sensestage/wearable_cape_v01/Documentation/Bela_Audio_Cape_Schematic.png

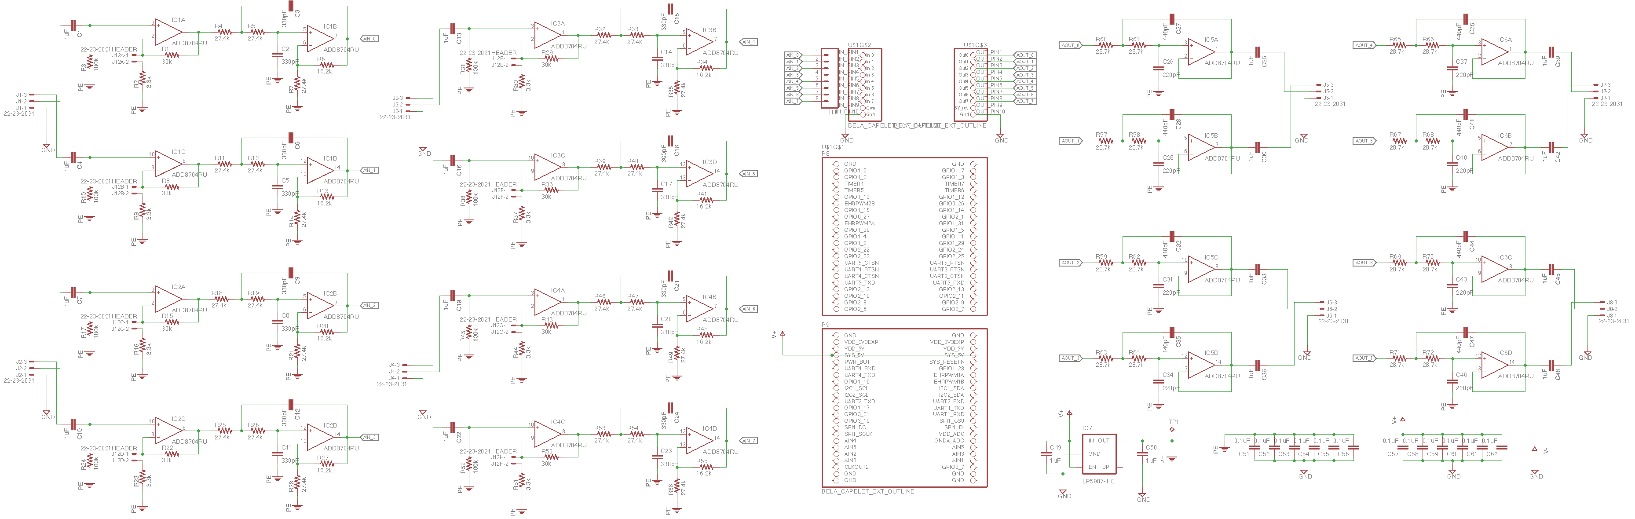
Documentation/Bela_Audio_Cape_Schematic.png
