sensestage/wearable_cape_v01/Documentation/Bela_Cape_Schematic01.png

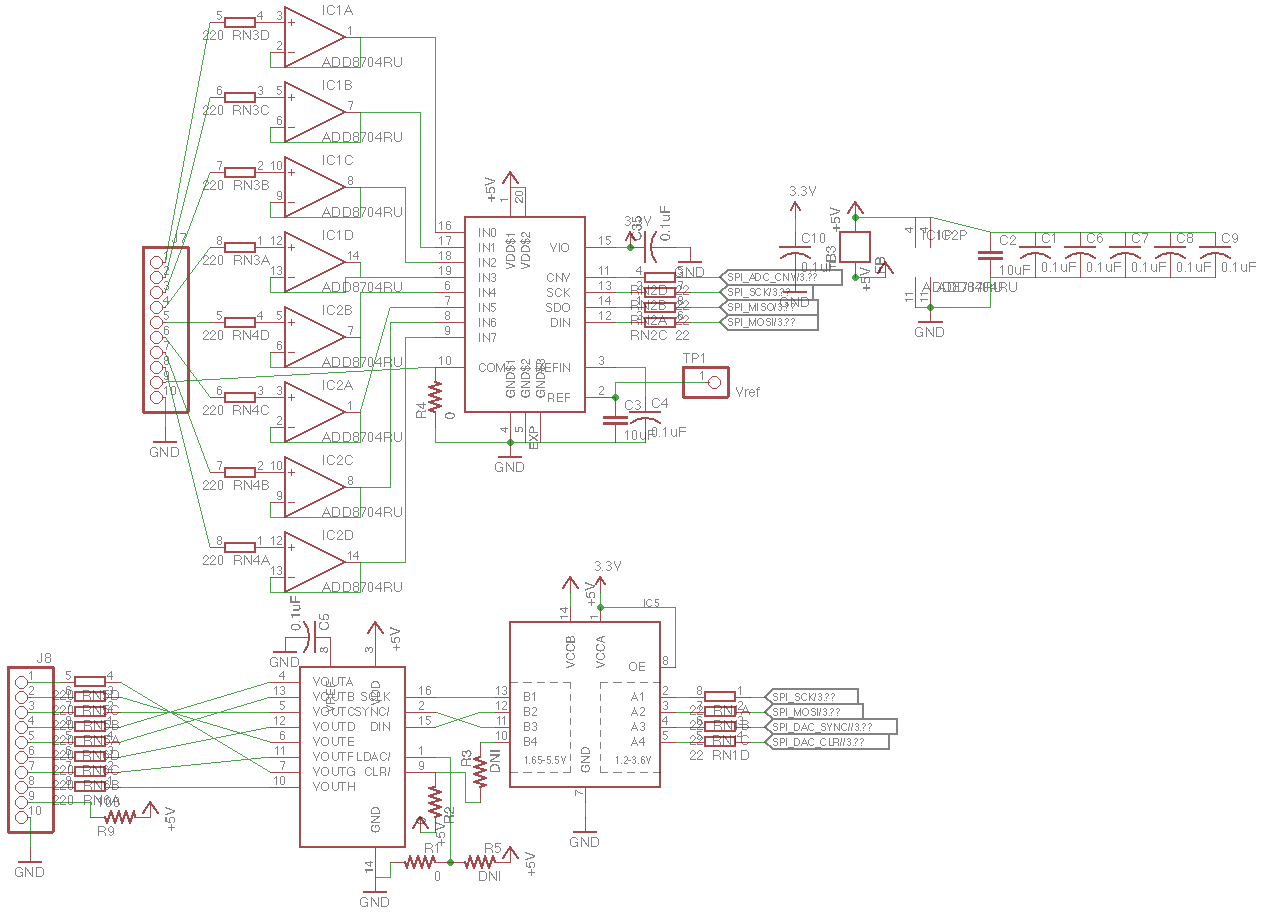
Documentation/Bela_Cape_Schematic01.png
