sensestage/wearable_cape_v01/Documentation/Datasheets/MAX9744_Adafruit_Inputs.png

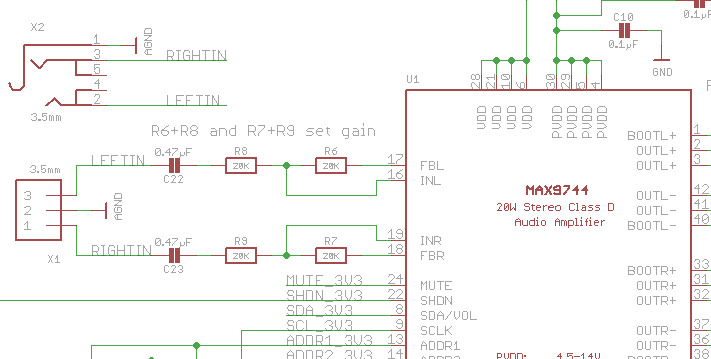
Documentation/Datasheets/MAX9744_Adafruit_Inputs.png
