sensestage/wearable_cape_v01/Documentation/Datasheets/MAX_9744_INPUTS.png

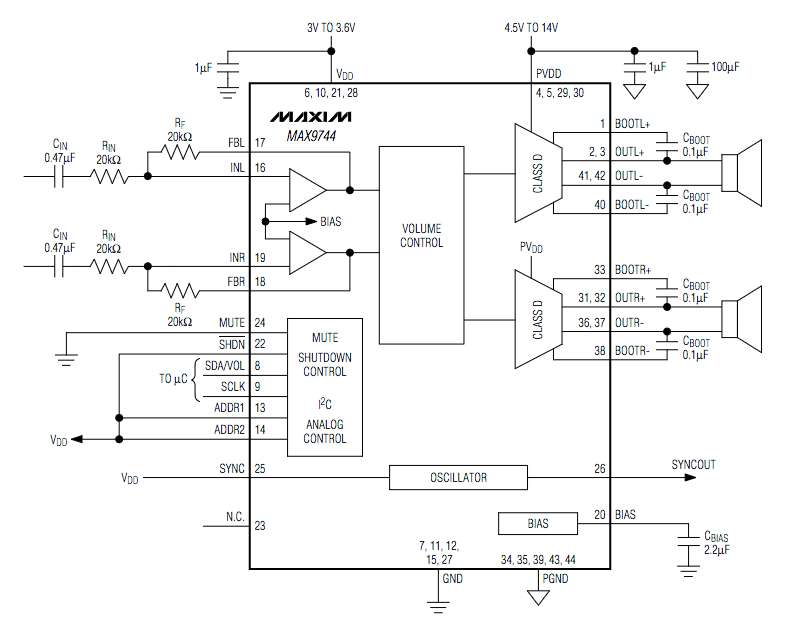
Documentation/Datasheets/MAX_9744_INPUTS.png
