sensestage/wearable_cape_v01/Documentation/earthquake_v01-PCB.png

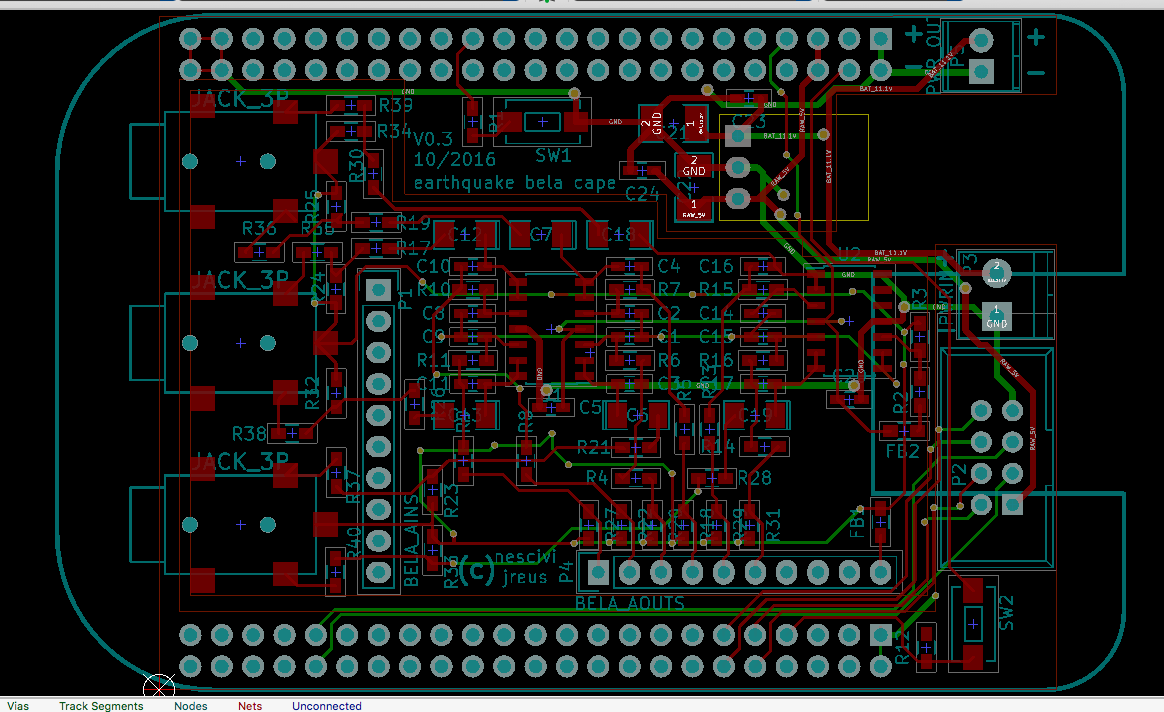
Documentation/earthquake_v01-PCB.png
