sensestage/wearable_cape_v01/Documentation/Simulations/Sallen-Key-Att-POST1.png

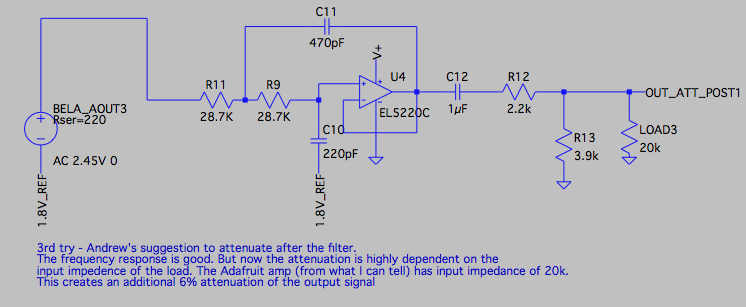
Documentation/Simulations/Sallen-Key-Att-POST1.png
