sensestage/wearable_cape_v01/Documentation/Simulations/Sallen-Key-Att-POST1_SER.png

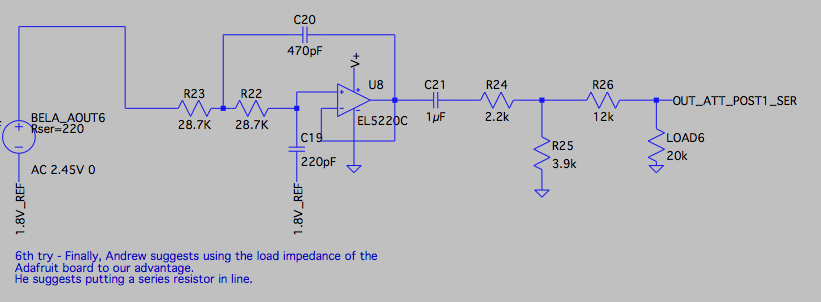
Documentation/Simulations/Sallen-Key-Att-POST1_SER.png
