sensestage/wearable_cape_v01/Documentation/Simulations/Sallen-Key-Att-PRE.png

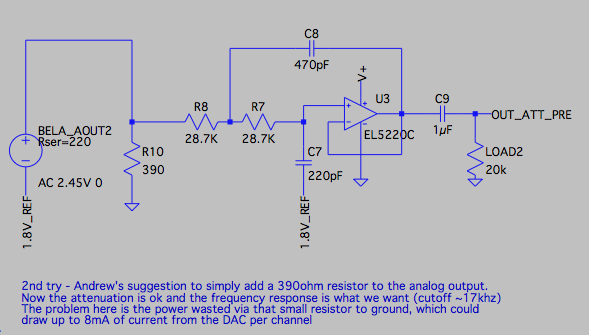
Documentation/Simulations/Sallen-Key-Att-PRE.png
